vojtechu-safarik/MCU_Synthesizer/MCU_Synthesizer/src/Hardware_Peripherals/HardwareKeyboard.cpp

#include <Arduino.h>

// === KEYPAD lib ===
#include "Keypad.h"
// ==================

// === GLOBAL VARIABLES ===
#include "Global_Variables/Global_Variables.h"
// ==================

// === CONFIGURATION ===
#include "Configuration/MIDI_Config.h"
#include "Configuration/Pins_Config.h"
// ==================

// === HARDWARE PERIPHERALS ===
#include "Hardware_Peripherals/HardwareKeyboard.h"
// ==================

// === SYNTHESIS FUNCTIONS ===
#include "Synthesis/Drone.h"
// ==================

/* === CONFIGURATION === */

/* SeqMode: 
    0 = Off
    1 = Arp
    2 = Latch
SeqOrder: 
    0 = Up
    1 = Down
    2 = Queue
SeqOctaves: 
    0 = 1 oct
    1 = 2 oct
    2 = 3 oct
SeqGatePot: 
    1 .. 100 
    ( how big portion of the step is the note in an active state )
SeqRateSelect:
    0 = 1/2 step length (BPM)
    1 = 1/4 step length (BPM)
    2 = 1/8 step length (BPM)
    3 = 1/16 step length (BPM)
*/

/* ===================== */

static const byte ROWS = 9;
static const byte COLS = 5;
static byte rowPins[ROWS] = {Row_1, Row_2, Row_3, Row_4, Row_5, Row_6, Row_7, Row_8, Row_9};
static byte colPins[COLS] = {Column_1, Column_2, Column_3, Column_4, Column_5};

static char keymap[ROWS][COLS] = {
  { 1,  2,  3,  4,  5},
  { 6,  7,  8,  9, 10},
  {11, 12, 13, 14, 15},
  {16, 17, 18, 19, 20},
  {21, 22, 23, 24, 25},
  {26, 27, 28, 29, 30}, 
  {31, 32, 33, 34, 35},
  {36, 37, 38, 39, 40},
  {41, 42, 43, 44, 45}
};

// MIDI notes: 254 = Rest (pause)
static const byte keyToMidiNote[45] = {
  // === Row 1 (Blue 1) ===
  0,   // [0] Column 1 (R1 B1): Oct Down
  56,  // [1] Column 2 (R2 B1): Note E3
  0,   // [2] Column 3 (R3 B1): (Shift)
  58,  // [3] Column 4 (R4 B1): Note F#3
  68,  // [4] Column 5 (R5 B1): Note E4 (Last Note)

  // === Row 2 (Blue 2) ===
  0,   // [5] Column 1 (R1 B2): Oct Up
  54,  // [6] Column 2 (R2 B2): Note D3
  0,   // [7] Column 3 (R3 B2): (LFO - Rise / Fall)
  60,  // [8] Column 4 (R4 B2): Note G#3
  67,  // [9] Column 5 (R5 B2): Note D#4

  // === Row 3 (Blue 3) ===
  40,  // [10] Column 1 (R1 B3): Note C2 (First Note)
  52,  // [11] Column 2 (R2 B3): Note C3
  0,   // [12] Column 3 (R3 B3): (LFO - Free / Trig)
  62,  // [13] Column 4 (R4 B3): Note A#3
  65,  // [14] Column 5 (R5 B3): Note C#4

  // === Row 4 (Blue 4) ===
  42,  // [15] Column 1 (R1 B4): Note D2
  51,  // [16] Column 2 (R2 B4): Note B2
  0,   // [17] Column 3 (R3 B4): Drone #1
  57,  // [18] Column 4 (R4 B4): Note F3
  0,   // [19] Column 5 (R5 B4): Drone #5

  // === Row 5 (Blue 5) ===
  44,  // [20] Column 1 (R1 B5): Note E2
  49,  // [21] Column 2 (R2 B5): Note A2
  0,   // [22] Column 3 (R3 B5): Drone #2
  59,  // [23] Column 4 (R4 B5): Note G3
  0,   // [24] Column 5 (R5 B5): Drone #6

  // === Row 6 (Blue 6) ===
  45,  // [25] Column 1 (R1 B6): Note F2
  47,  // [26] Column 2 (R2 B6): Note G2
  0,   // [27] Column 3 (R3 B6): Drone #3
  61,  // [28] Column 4 (R4 B6): Note A3
  0,   // [29] Column 5 (R5 B6): Drone #7

  // === Row 7 (Blue 7) ===
  0,   // [30] Column 1 (R1 B7): (Unused)
  50,  // [31] Column 2 (R2 B7): Note A#2
  0,   // [32] Column 3 (R3 B7): Drone #4
  63,  // [33] Column 4 (R4 B7): Note B3
  0,   // [34] Column 5 (R5 B7): Drone #8

  // === Row 8 (Blue 8) ===
  41,  // [35] Column 1 (R1 B8): Note C#2
  48,  // [36] Column 2 (R2 B8): Note G#2
  53,  // [37] Column 3 (R3 B8): Note C#3
  64,  // [38] Column 4 (R4 B8): Note C4
  0,   // [39] Column 5 (R5 B8): (Unused)

  // === Row 9 (Blue 9) ===
  43,  // [40] Column 1 (R1 B9): Note D#2
  46,  // [41] Column 2 (R2 B9): Note F#2
  55,  // [42] Column 3 (R3 B9): Note D#3
  66,  // [43] Column 4 (R4 B9): Note D4
  0    // [44] Column 5 (R5 B9): (Unused)
};

static const byte keyToLFOWave[45] = {
  255, 255, 255, 255, 255,
  255, 255, 255, 255, 255,
    0, 255, 255, 255, 255,
    1, 255, 255, 255, 255,
    2, 255, 255, 255, 255,
    3,   4, 255, 255, 255,
  255, 255, 255, 255, 255,
  255, 255, 255, 255, 255,
  255, 255, 255, 255, 255
};

static const byte keyToPORTlockRate[45] = {
  255, 255, 255, 255, 255,
  255, 255, 255, 255, 255,
  255, 255, 255, 255, 255,
  255, 255, 255, 255, 255,
  255, 255, 255, 255, 255,
  255, 255, 255, 255, 255,
  255,   4, 255, 255, 255,
    0,   3, 255, 255, 255,
    1,   2, 255, 255, 255
};

static const byte keyRest[45] = {
  255, 255, 255, 255, 255,
  255, 255, 255, 255, 255,
  255, 255, 255, 255, 255,
  255, 255,   0, 255, 255,
  255, 255, 255, 255, 255,
  255, 255, 255, 255, 255,
  255, 255, 255, 255, 255,
  255, 255, 255, 255, 255,
  255, 255, 255, 255, 255
};

static const byte keyUnisonTriadToggle[45] = {
  255, 255, 255, 255,   0,
  255, 255, 255, 255, 255,
  255, 255, 255, 255, 255,
  255, 255, 255, 255, 255,
  255, 255, 255, 255, 255,
  255, 255, 255, 255, 255,
  255, 255, 255, 255, 255,
  255, 255, 255, 255, 255,
  255, 255, 255, 255, 255
};

static const byte keyToDrone[45] = {
  255, 255, 255, 255, 255,
  255, 255, 255, 255, 255,
  255, 255, 255, 255, 255,
  255, 255, 91,  255, 95, 
  255, 255, 92,  255, 96, 
  255, 255, 93,  255, 97,  
  255, 255, 94,  255, 98,
  255, 255, 255, 255, 255,
  255, 255, 255, 255, 255
};

static constexpr byte HW_CHANNEL  = 0;
static constexpr byte HW_VELOCITY = 127;

static constexpr byte KEY_OCT_DOWN   = 0;
static constexpr byte KEY_OCT_UP     = 5;
static constexpr byte KEY_SHIFT      = 2;

/* ================== STATE VARIABLES ================== */

static Keypad keypad = Keypad(makeKeymap(keymap), rowPins, colPins, ROWS, COLS);

static int activeKeyStack[256];  // Amount of notes in Latch
static byte activeKeyCount = 0;
static int playingNotes[45];     // Tracking the notes in Direct Play for immediate transposition

int sequenceBuffer[256];
byte sequenceLength = 0;

static unsigned long internal_lastStepTime = 0;
static int internal_currentlyPlayingNote = -1;
static unsigned long internal_gateOffTime = 0;
static byte internal_playHead = 0; 

static bool shiftActive = false;

// Sequencer step length modifier variables
static byte nextNoteLenCode = 4; // 4 = 1.0x, 8 = 2.0x, 16 = 4.0x, 2 = 0.5x, 1 = 0.25x
static float currentStepDurationMult = 1.0;

int octaveValue = 2; 

/* ================== HELPERS ================== */

void internal_stopNote() {
    if (internal_currentlyPlayingNote >= 0) {
        myNoteOff(HW_CHANNEL, (byte)internal_currentlyPlayingNote, 0);
        internal_currentlyPlayingNote = -1;
    }
}

// Immediately change the pitch of Direct play
void updateDirectPlayOctave() {
    if (CurrentSeqMode != 0) return; 
    // Loop through all possible keys instead of bounded notes
    for (int i = 0; i < 45; i++) {
        if (playingNotes[i] != -1) {
            myNoteOff(HW_CHANNEL, (byte)playingNotes[i], 0);
            int newNote = keyToMidiNote[i] + ((octaveValue - 2) * 12);
            if (newNote < 0) newNote = 0; if (newNote > 127) newNote = 127;
            playingNotes[i] = newNote;
            myNoteOn(HW_CHANNEL, (byte)newNote, HW_VELOCITY);
        }
    }
}

void pushKey(byte keyIndex, bool isRest = false) {
    // Arp mode (1) doesnt support duplicities
    if (CurrentSeqMode == 1) {
        for (byte i = 0; i < activeKeyCount; i++) {
            // Mask bits 0-6 to check only the physical key index
            if ((activeKeyStack[i] & 0x7F) == keyIndex) return; 
        }
    }
    
    // Latch mode (2) can have the same notes in a row
    if (activeKeyCount < 255) {
        // Encode: [Length Code: 8 bits] [isRest: 1 bit] [KeyIndex: 7 bits]
        int packedValue = (nextNoteLenCode << 8) | (isRest ? 0x80 : 0) | (keyIndex & 0x7F);
        activeKeyStack[activeKeyCount++] = packedValue;
        nextNoteLenCode = 4; // Reset to normal length after use
    }
}

void popKey(byte keyIndex) {
    bool found = false;
    for (byte i = 0; i < activeKeyCount; i++) {
        // Compare only the physical index (bits 0-6)
        if ((activeKeyStack[i] & 0x7F) == keyIndex) found = true;
        if (found && i < activeKeyCount - 1) activeKeyStack[i] = activeKeyStack[i+1];
    }
    if (found && activeKeyCount > 0) activeKeyCount--;
}

static unsigned long shiftPressTime = 0;
static bool latchCleared = false;

/* ================== SEQUENCER LOGIC ================== */

void rebuildSequence() {
    sequenceLength = 0;
    if (activeKeyCount == 0) return;

    int tempNotes[256];
    for (byte i = 0; i < activeKeyCount; i++) {
        byte keyIdx = activeKeyStack[i] & 0x7F;
        bool isRest = (activeKeyStack[i] & 0x80) != 0;
        byte lenCode = (activeKeyStack[i] >> 8) & 0xFF;
        
        // Use 254 if marked as rest, else look up standard MIDI mapping
        int midiNote = isRest ? 254 : keyToMidiNote[keyIdx];
        tempNotes[i] = (lenCode << 8) | midiNote;
    }

    // Sort for UP/DOWN (Queue mode 2 is being skipped)
    if (CurrentSeqOrder < 2) {
        for (byte i = 0; i < activeKeyCount; i++) {
            for (byte j = i + 1; j < activeKeyCount; j++) {
                if ((tempNotes[j] & 0xFF) < (tempNotes[i] & 0xFF)) {
                    int t = tempNotes[i]; tempNotes[i] = tempNotes[j]; tempNotes[j] = t;
                }
            }
        }
        if (CurrentSeqOrder == 1) { // Down
            for (byte i = 0; i < activeKeyCount / 2; i++) {
                int t = tempNotes[i];
                tempNotes[i] = tempNotes[activeKeyCount - 1 - i];
                tempNotes[activeKeyCount - 1 - i] = t;
            }
        }
    }

    // Expansion + Final Buffer
    for (byte i = 0; i < activeKeyCount; i++) {
        int base = tempNotes[i] & 0xFF;
        byte lenCode = (tempNotes[i] >> 8) & 0xFF;
        for (byte r = 0; r <= CurrentSeqOctave; r++) {
            if (sequenceLength < 256) {
                // If pause (254), dont increment octaves
                int finalNote = (base == 254) ? 254 : (base + (r * 12));
                sequenceBuffer[sequenceLength++] = (lenCode << 8) | finalNote;
            }
        }
    }
}

void internal_sequencerUpdate() {
    if (CurrentSeqMode == 0) return;

    unsigned long now = millis();

    if (internal_currentlyPlayingNote >= 0 && internal_gateOffTime > 0 && now >= internal_gateOffTime) {
        internal_stopNote();
        internal_gateOffTime = 0;
    }

    int bpm = (GlobalBPM < 1) ? 120 : GlobalBPM;
    unsigned long stepMs = 60000UL / bpm; 

    if (SeqRateSelect == 0) stepMs *= 2;
    else if (SeqRateSelect == 2) stepMs /= 2;
    else if (SeqRateSelect == 3) stepMs /= 4;

    // Evaluate step wait time using current step's duration multiplier
    if ((now - internal_lastStepTime) < (unsigned long)(stepMs * currentStepDurationMult)) return;
    internal_lastStepTime = now;

    rebuildSequence();
    if (sequenceLength == 0) {
        internal_playHead = 0;
        return;
    }

    if (internal_playHead >= sequenceLength) internal_playHead = 0;

    int rawData = sequenceBuffer[internal_playHead];
    int rawNote = rawData & 0xFF;
    byte lenCode = (rawData >> 8) & 0xFF;

    // Decode length byte to float multiplier for THIS specific note
    if (lenCode == 1) currentStepDurationMult = 0.25;
    else if (lenCode == 2) currentStepDurationMult = 0.5;
    else if (lenCode == 4) currentStepDurationMult = 1.0;
    else if (lenCode == 8) currentStepDurationMult = 2.0;
    else if (lenCode == 16) currentStepDurationMult = 4.0;
    else currentStepDurationMult = 1.0;

    internal_stopNote();

    if (rawNote == 254) {
        internal_currentlyPlayingNote = -1; // pause
    } else {
        int finalNote = rawNote + ((octaveValue - 2) * 12);
        if (finalNote < 0) finalNote = 0; if (finalNote > 127) finalNote = 127;
        internal_currentlyPlayingNote = finalNote;
        myNoteOn(HW_CHANNEL, (byte)finalNote, HW_VELOCITY);
    }

    // Gate length naturally scales with the stretched step duration
    internal_gateOffTime = now + (unsigned long)((stepMs * currentStepDurationMult) * SeqGatePot / 100);
    internal_playHead++;
}

/* ================== CORE LOOP ================== */

/* ================== CORE LOOP ================== */

void Keyboard_init() {
    for(int i=0; i<45; i++) playingNotes[i] = -1;
    activeKeyCount = 0;
    internal_lastStepTime = millis();
    nextNoteLenCode = 4; // Start at normal 1.0x length
    currentStepDurationMult = 1.0;
}

void Keyboard_update() {
    // 1. Sequencer must run all the time
    internal_sequencerUpdate();

    if (shiftActive && !latchCleared && (millis() - shiftPressTime > 3000)) {
        activeKeyCount = 0; 
        latchCleared = true; 
    }

    // 3. Change checking for keyboard
    if (!keypad.getKeys()) return;

    for (byte i = 0; i < LIST_MAX; i++) {
        if (!keypad.key[i].stateChanged) continue;
        
        byte index = keypad.key[i].kchar - 1; 
        if (index >= 45) continue;

        switch (keypad.key[i].kstate) {
            case PRESSED:
                if (index == KEY_SHIFT) {
                    shiftActive = true;
                    shiftPressTime = millis();
                    latchCleared = false;
                    break;
                }

                // --- SHIFT LOGIC ---
                if (shiftActive) {
                    
                    // LFO Free/Trig (index 12) -> Extend next note duration
                    if (index == 12) {
                        if (nextNoteLenCode < 16) nextNoteLenCode *= 2; 
                        break;
                    }
                    // LFO Rise/Fall (index 7) -> Shorten next note duration
                    if (index == 7) { 
                        if (nextNoteLenCode > 1) nextNoteLenCode /= 2;
                        break; 
                    }

                    // Check for Rest Entry using keyRest map
                    if (keyRest[index] != 255) {
                        if (CurrentSeqMode > 0) {
                            pushKey(index, true); // true = push as REST
                        }
                        break;
                    }

                    // LFO Wave selection
                    if (keyToLFOWave[index] != 255) {
                        VirtualControlChange(0, CC_LFOwaveSelect, keyToLFOWave[index]);
                    }
                    // Portamento/Lock Rate
                    if (keyToPORTlockRate[index] != 255) {
                        VirtualControlChange(0, CC_PORTlockRate, keyToPORTlockRate[index]);
                    }

                    // unisonTriadToggle
                    if (index == 4) {
                        static byte unisonTriadState = 0; // static, doesnt dissapear after loop
                        TriadToggleFlag = !TriadToggleFlag; // to remember the set option before activating portamento when it gets turned off again
                        unisonTriadState = !unisonTriadState;
                        VirtualControlChange(0, CC_unisonTriadToggle, unisonTriadState);
                    }
                    
                    // Seq Rate Increment/Decrement
                    if (index == KEY_OCT_DOWN) {
                        if (SeqRateSelect > 0) SeqRateSelect--;
                    }
                    if (index == KEY_OCT_UP) {
                        if (SeqRateSelect < 3) SeqRateSelect++;
                    }
                    break;
                }

                // --- NORMAL LOGIC ---
                if (index == KEY_OCT_DOWN) {
                    if (octaveValue > 0) {
                        octaveValue--;
                        // if (CurrentSeqMode == 0) VirtualControlChange(0, CC_octave, octaveValue);
                    }
                } 
                else if (index == KEY_OCT_UP) {
                    if (octaveValue < 4) {
                        octaveValue++;
                        // if (CurrentSeqMode == 0) VirtualControlChange(0, CC_octave, octaveValue);
                    }
                } 
                else if (!shiftActive) {
                    // --- DRONE KEY CHECK ---
                    if (keyToDrone[index] != 255) {
                        // Posíláme CC 91-98 s hodnotou 1 (Pressed)
                        VirtualControlChange(0, keyToDrone[index], 1);
                    }

                    // --- REGULAR NOTE CHECK ---
                    byte note = keyToMidiNote[index];
                    if (note > 0 && note < 128) {
                        if (CurrentSeqMode > 0) {
                            pushKey(index, false);
                        } else {
                            playingNotes[index] = note + ((octaveValue - 2) * 12);
                            myNoteOn(HW_CHANNEL, (byte)playingNotes[index], HW_VELOCITY);
                        }
                    }
                }
                
                // Triggers from normal logic (Upraveno, aby Shift neaktivoval LFO přepínání)
                if (!shiftActive) {
                    if (index == 12) { // Free / Trig
                        LFOmodeSelect = (LFOmodeSelect >= 2) ? 0 : (1 - LFOmodeSelect);
                    }
                    else if (index == 7) { // Rise / Fall
                        LFOmodeSelect = (LFOmodeSelect < 2) ? 2 : (LFOmodeSelect == 2 ? 3 : 2);
                    }
                }
                break;

            case RELEASED:
                if (index == KEY_SHIFT) {
                    shiftActive = false;
                    shiftPressTime = 0;
                } 
                else if (index != KEY_OCT_DOWN && index != KEY_OCT_UP) {
                    // --- DRONE RELEASE CHECK ---
                    if (keyToDrone[index] != 255) {
                        VirtualControlChange(0, keyToDrone[index], 0);
                        // Pokud je v Arp módu Rest (index 17), popKey ho uklidí níže
                    }

                    // Safe cleanup: Try to pop by physical index regardless of what it was
                    // (helps prevent stuck keys if Shift is released mid-press)
                    if (CurrentSeqMode == 1) {
                        popKey(index);
                    } else if (CurrentSeqMode == 0) {
                        if (playingNotes[index] != -1) {
                            myNoteOff(HW_CHANNEL, (byte)playingNotes[index], 0);
                            playingNotes[index] = -1;
                        }
                    }
                }
                break;
        }
    }
}
