vojtechu-safarik/MCU_Synthesizer/Wavetable scripts/Python/03 - Triangle/Triangle_Wavetables.h

#ifndef CUSTOM_TRIANGLE_WAVETABLES_H
#define CUSTOM_TRIANGLE_WAVETABLES_H

#include <stdint.h>

const int16_t triangle1[256] = {
     32767,  32255,  31743,  31231,  30719,  30207,  29695,  29183,
     28671,  28159,  27647,  27135,  26623,  26111,  25599,  25087,
     24575,  24063,  23551,  23039,  22527,  22015,  21503,  20991,
     20479,  19967,  19455,  18943,  18431,  17919,  17407,  16895,
     16383,  15871,  15359,  14847,  14335,  13823,  13311,  12799,
     12287,  11775,  11263,  10751,  10239,   9727,   9215,   8703,
      8191,   7679,   7167,   6655,   6143,   5631,   5119,   4607,
      4095,   3583,   3071,   2559,   2047,   1535,   1023,    511,
         0,   -511,  -1023,  -1535,  -2047,  -2559,  -3071,  -3583,
     -4095,  -4607,  -5119,  -5631,  -6143,  -6655,  -7167,  -7679,
     -8191,  -8703,  -9215,  -9727, -10239, -10751, -11263, -11775,
    -12287, -12799, -13311, -13823, -14335, -14847, -15359, -15871,
    -16383, -16895, -17407, -17919, -18431, -18943, -19455, -19967,
    -20479, -20991, -21503, -22015, -22527, -23039, -23551, -24063,
    -24575, -25087, -25599, -26111, -26623, -27135, -27647, -28159,
    -28671, -29183, -29695, -30207, -30719, -31231, -31743, -32255,
    -32767, -32255, -31743, -31231, -30719, -30207, -29695, -29183,
    -28671, -28159, -27647, -27135, -26623, -26111, -25599, -25087,
    -24575, -24063, -23551, -23039, -22527, -22015, -21503, -20991,
    -20479, -19967, -19455, -18943, -18431, -17919, -17407, -16895,
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
    -18203, -10922,   3640, -10922,  10922, -18203,  -3640,  10922,
     -3640, -18203, -10922,  -3640, -18203, -18203, -10922,   3640,
    -25485,  -3640, -10922,   3640, -10922, -18203, -18203, -18203,
     10922,  18203,  25485,  18203, -10922, -18203,  -3640,  18203,
};
#endif // CUSTOM_TRIANGLE_WAVETABLES_H
